jaylogue/pdp1105-console-adapter-v2/pcb/pdp1105-console-adapter-v2-pcb-3d-back.png

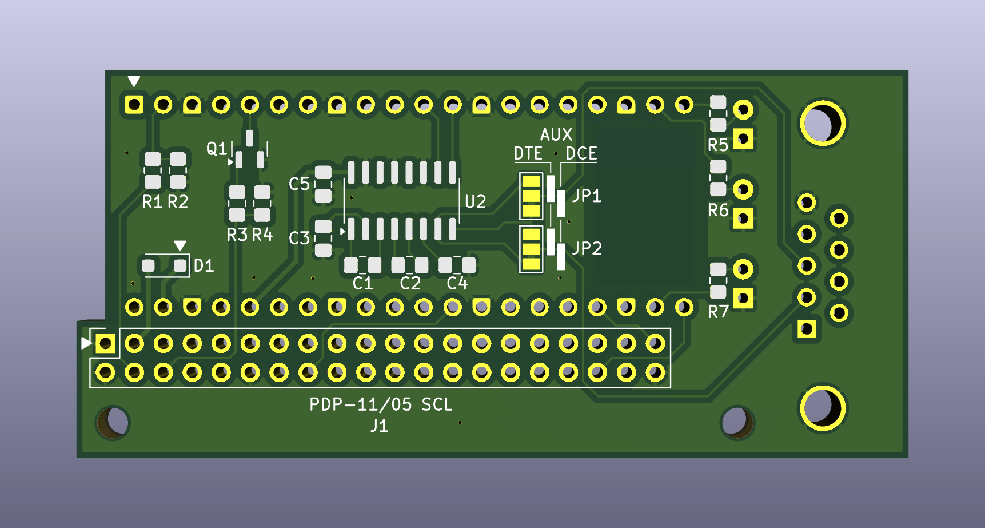
pcb/pdp1105-console-adapter-v2-pcb-3d-back.png
