jaylogue/pdp1105-console-adapter-v2/src/SCLPort.cpp

/*
 * Copyright 2024-2025 Jay Logue
 * 
 * Licensed under the Apache License, Version 2.0 (the "License");
 * you may not use this file except in compliance with the License.
 * You may obtain a copy of the License at
 * 
 *     http://www.apache.org/licenses/LICENSE-2.0
 * 
 * Unless required by applicable law or agreed to in writing, software
 * distributed under the License is distributed on an "AS IS" BASIS,
 * WITHOUT WARRANTIES OR CONDITIONS OF ANY KIND, either express or implied.
 * See the License for the specific language governing permissions and
 * limitations under the License.
 */

#include "ConsoleAdapter.h"

#include "hardware/clocks.h"
#include "hardware/pwm.h"
#include "hardware/uart.h"

SCLPort gSCLPort;

SerialConfig SCLPort::sConfig = { SCL_DEFAULT_BAUD_RATE, 8, 2, SerialConfig::PARITY_NONE };
bool SCLPort::sReaderRunRequested;
uint64_t SCLPort::sRXInactiveTime;

void SCLPort::Init(void)
{
    // Setup the SCL UART
    uart_init(SCL_UART, sConfig.BitRate);
    uart_set_fifo_enabled(SCL_UART, true);
    gpio_set_function(SCL_UART_RX_PIN, UART_FUNCSEL_NUM(SCL_UART, SCL_UART_RX_PIN));
    gpio_set_function(SCL_UART_TX_PIN, UART_FUNCSEL_NUM(SCL_UART, SCL_UART_TX_PIN));

    // Setup the SCL clock generator
    uint slice = pwm_gpio_to_slice_num(SCL_CLOCK_PIN);
    gpio_set_function(SCL_CLOCK_PIN, GPIO_FUNC_PWM);
    pwm_set_clkdiv_int_frac(slice, PWM_DIVISOR_INT, PWM_DIVISOR_FRACT);
    ConfigSCLClock(sConfig.BitRate);
    pwm_set_enabled(pwm_gpio_to_slice_num(SCL_CLOCK_PIN), true);

    // Configure the SCL UART
    SetConfig(sConfig);

    // Initialize the SCL detect pin
    //
    // NOTE: The SCL detect input is active-low, i.e. a low (GND) value
    // indicates the SCL port is connected.  As a convenience,
    // GPIO_OVERRIDE_INVERT is used to make the connected state appear
    // as 1 when read by gpio_get().
    gpio_init(SCL_DETECT_PIN);
    gpio_set_dir(SCL_DETECT_PIN, GPIO_IN);
    gpio_set_inover(SCL_DETECT_PIN, GPIO_OVERRIDE_INVERT);
    gpio_set_irqover(SCL_DETECT_PIN, GPIO_OVERRIDE_INVERT);
    gpio_pull_up(SCL_DETECT_PIN);

    // Initialize the READER_RUN input pin and arrange to receive an 
    // interrupt when it transitions to active.
    //
    // NOTE: As seen by the Pico, the READER_RUN input is active-low, i.e.
    // a low (GND) value on the READER_RUN pin indicates the PDP-11 has
    // activated its READER RUN + output.  As a convenience, 
    // GPIO_OVERRIDE_INVERT is used to make the active state appear as 1
    // when read by gpio_get().
    gpio_init(READER_RUN_PIN);
    gpio_set_dir(READER_RUN_PIN, GPIO_IN);
    gpio_set_inover(READER_RUN_PIN, GPIO_OVERRIDE_INVERT);
    gpio_set_irqover(READER_RUN_PIN, GPIO_OVERRIDE_INVERT);
    gpio_pull_up(READER_RUN_PIN);
    gpio_add_raw_irq_handler(READER_RUN_PIN, HandleReaderRunIRQ);
    gpio_set_irq_enabled(READER_RUN_PIN, GPIO_IRQ_EDGE_RISE, true);
    irq_set_enabled(IO_IRQ_BANK0, true);
}

void SCLPort::SetConfig(const SerialConfig& serialConfig)
{
    // Wait for the UART transmission queue to empty.
    Flush();

    // Accept the new configuration.
    sConfig = serialConfig;

    // The SCL port on the PDP11/05 is hard-wired to use 2 stop bits, so
    // force the use of 2 stop bits here.
    sConfig.StopBits = 2;

    // Set the baud rate and format for the SCL UART
    uart_set_baudrate(SCL_UART, serialConfig.BitRate);
    uart_set_format(SCL_UART, serialConfig.DataBits, serialConfig.StopBits, (uart_parity_t)serialConfig.Parity);

    // The SCL clock based on the new serial configuration.
    ConfigSCLClock(serialConfig.BitRate);
}

bool SCLPort::IsConnected(void)
{
    return gpio_get(SCL_DETECT_PIN);
}

bool SCLPort::IsPowered(void)
{
    // The PDP-11 is powered if the RX pin is currently active, or if
    // the RX pin has been inactive for less than kUnpoweredTimeoutUS.
    return sRXInactiveTime == 0 || time_us_64() < (sRXInactiveTime + kUnpoweredTimeoutUS);
}

void SCLPort::UpdateState(void)
{
    // The PDP-11/05 SCL port expects the SERIAL IN (TTL) signal (pin
    // RR/36) to use inverted signaling (i.e. 0V = MARK, +V = SPACE).
    // However, when the console adapter is not connected to the SCL
    // port, it is convenient to use normal signaling so that a
    // loopback test can be performed by jumpering pins RR/36 and D/04
    // on SCL connector.

    // If the console adapter is connected to the PDP-11's SCL port,
    // configure the SCL UART TX pin to output serial data in inverted
    // format. Otherwise, use normal TX signaling.
    gpio_set_outover(SCL_UART_TX_PIN, IsConnected() ? GPIO_OVERRIDE_INVERT : GPIO_OVERRIDE_NORMAL);

    // The power state of the PDP-11 is determined by monitoring
    // activity on the SCL UART RX pin. If the RX pin is active
    // (high), then the PDP-11 has power. If the RX pin is inactive
    // (low), it could mean: 1) the PDP-11 is unpowered, or 2) the
    // SCL UART is receiving a character.
    //
    // To differentiate the two cases, the code tracks how long the
    // RX pin stays inactive. If the RX pin is inactive for an
    // extended period (kUnpoweredTimeoutUS), and no characters are
    // received during that period, then the PDP-11 is considered
    // to be unpowered.

    // Check the current state of the SCL UART RX pin.
    // If the RX pin is active (high), implying then the PDP-11 has
    // power, then clear the RX inactive time. Otherwise, mark the
    // time at which the RX pin was first observed to be inactive.
    if (gpio_get(SCL_UART_RX_PIN)) {
        sRXInactiveTime = 0;
    }
    else if (sRXInactiveTime == 0) {
        sRXInactiveTime = time_us_64();
    }
}

void SCLPort::ConfigSCLClock(uint32_t bitRate)
{
    // Compute the SCL clock rate from the configured baud rate.
    uint32_t sclClockRate = bitRate * 16;

    // Compute the divisor needed to produce the SCL clock from the
    // system's peripheral clock.
    float sclClockDiv = ((float)clock_get_hz(clk_peri)) / sclClockRate;

    // Compute the PWM counter wrap value needed to generate the
    // target SCL clock rate given the configured PWM divisor.
    constexpr float pwmDiv = PWM_DIVISOR_INT + (PWM_DIVISOR_FRACT / 16.0F);
    uint16_t pwmWrapValue = (uint16_t)((sclClockDiv / pwmDiv) + 0.5) - 1;

    // Set the PWM wrap register to the computed value.
    pwm_set_wrap(pwm_gpio_to_slice_num(SCL_CLOCK_PIN), pwmWrapValue);

    // Set the PWM comparator value (a.k.a. "level") to half the wrap
    // value (i.e. 50% duty cycle).
    pwm_set_gpio_level(SCL_CLOCK_PIN, (pwmWrapValue + 1) / 2);
}

void SCLPort::HandleReaderRunIRQ(void)
{
    if ((gpio_get_irq_event_mask(READER_RUN_PIN) & GPIO_IRQ_EDGE_RISE) != 0) {
        gpio_acknowledge_irq(READER_RUN_PIN, GPIO_IRQ_EDGE_RISE);
        sReaderRunRequested = true;
    }
}
