jaylogue/pdp1105-console-adapter-v2/src/SCLPort.h

/*
 * Copyright 2024-2025 Jay Logue
 * 
 * Licensed under the Apache License, Version 2.0 (the "License");
 * you may not use this file except in compliance with the License.
 * You may obtain a copy of the License at
 * 
 *     http://www.apache.org/licenses/LICENSE-2.0
 * 
 * Unless required by applicable law or agreed to in writing, software
 * distributed under the License is distributed on an "AS IS" BASIS,
 * WITHOUT WARRANTIES OR CONDITIONS OF ANY KIND, either express or implied.
 * See the License for the specific language governing permissions and
 * limitations under the License.
 */

#ifndef SCL_PORT_H
#define SCL_PORT_H

struct SerialConfig;

class SCLPort final : public Port
{
public:
    SCLPort(void) = default;
    virtual ~SCLPort(void) = default;

    SCLPort(const SCLPort&) = delete;
    SCLPort& operator=(const SCLPort&) = delete;

    void Init(void);
    const SerialConfig& GetConfig(void);
    void SetConfig(const SerialConfig& serialConfig);
    bool IsConnected(void);
    bool IsPowered(void);
    bool ReaderRunRequested(void);
    void ClearReaderRunRequested(void);
    void UpdateState(void);

    virtual char Read(void);
    virtual bool TryRead(char &ch);
    virtual void Write(char ch);
    virtual void Write(const char * str);
    virtual void Flush(void);
    virtual bool CanWrite(void);

    static constexpr uint32_t kUnpoweredTimeoutUS = 250000;

private:
    static SerialConfig sConfig;
    static bool sReaderRunRequested;
    static uint64_t sRXInactiveTime;

    static void ConfigSCLClock(uint32_t bitRate);
    static void HandleReaderRunIRQ(void);
};

extern SCLPort gSCLPort;

inline const SerialConfig& SCLPort::GetConfig(void)
{
    return sConfig;
}

inline bool SCLPort::ReaderRunRequested(void)
{
    return sReaderRunRequested;
}

inline void SCLPort::ClearReaderRunRequested(void)
{
    sReaderRunRequested = false;
}

inline char SCLPort::Read(void)
{
    char ch = uart_getc(SCL_UART);
    sRXInactiveTime = 0;
    ActivityLED::TxActive();
    ActivityLED::SysActive();
    return ch;
}

inline bool SCLPort::TryRead(char& ch)
{
    if (uart_is_readable(SCL_UART)) {
        ch = uart_getc(SCL_UART);
        sRXInactiveTime = 0;
        ActivityLED::TxActive();
        ActivityLED::SysActive();
        return true;
    }
    return false;
}

inline void SCLPort::Write(char ch)
{
    uart_putc(SCL_UART, ch);
    ActivityLED::RxActive();
    ActivityLED::SysActive();
}

inline void SCLPort::Write(const char* str)
{
    uart_puts(SCL_UART, str);
    ActivityLED::RxActive();
    ActivityLED::SysActive();
}

inline void SCLPort::Flush(void)
{
    uart_tx_wait_blocking(SCL_UART);
}

inline bool SCLPort::CanWrite(void)
{
    return uart_is_writable(SCL_UART);
}

#endif // SCL_PORT_H
