jaylogue/pdp1105-console-adapter-v2/src/Utils.cpp

/*
 * Copyright 2024-2025 Jay Logue
 * 
 * Licensed under the Apache License, Version 2.0 (the "License");
 * you may not use this file except in compliance with the License.
 * You may obtain a copy of the License at
 * 
 *     http://www.apache.org/licenses/LICENSE-2.0
 * 
 * Unless required by applicable law or agreed to in writing, software
 * distributed under the License is distributed on an "AS IS" BASIS,
 * WITHOUT WARRANTIES OR CONDITIONS OF ANY KIND, either express or implied.
 * See the License for the specific language governing permissions and
 * limitations under the License.
 */

#include <stdarg.h>
#include <pico/printf.h>

#include "ConsoleAdapter.h"

int Port::Printf(const char* format, ...)
{
    va_list args;
    va_start(args, format);
    
    // Create a local lambda to write each character to this port
    auto write_char = [](char ch, void* arg) -> void {
        Port* port = static_cast<Port*>(arg);
        port->Write(ch);
    };
    
    // Use vfctprintf from Pico SDK to format and output the string
    int result = vfctprintf(write_char, this, format, args);
    
    va_end(args);
    return result;
}

bool TryReadHostAuxPorts(char& ch) 
{
    return gHostPort.TryRead(ch)
#if defined(AUX_TERM_UART)
        || gAuxPort.TryRead(ch)
#endif
    ;
}

bool TryReadHostAuxPorts(char& ch, Port *& port)
{
    if (gHostPort.TryRead(ch)) {
        port = &gHostPort;
        return true;
    }

#if defined(AUX_TERM_UART)
    if (gAuxPort.TryRead(ch)) {
        port = &gAuxPort;
        return true;
    }
#endif

    port = NULL;
    return false;
}

void WriteHostAuxPorts(char ch)
{
    gHostPort.Write(ch);
#if defined(AUX_TERM_UART)
    gAuxPort.Write(ch);
#endif
}

void WriteHostAuxPorts(const char* str)
{
    gHostPort.Write(str);
#if defined(AUX_TERM_UART)
    gAuxPort.Write(str);
#endif
}
